so1der/ivl275_clock/ivl275_schematic/ivl275_clock.kicad_sch

## KiCad design ivl275_schematic/ivl275_clock.kicad_sch (2024-07-03)

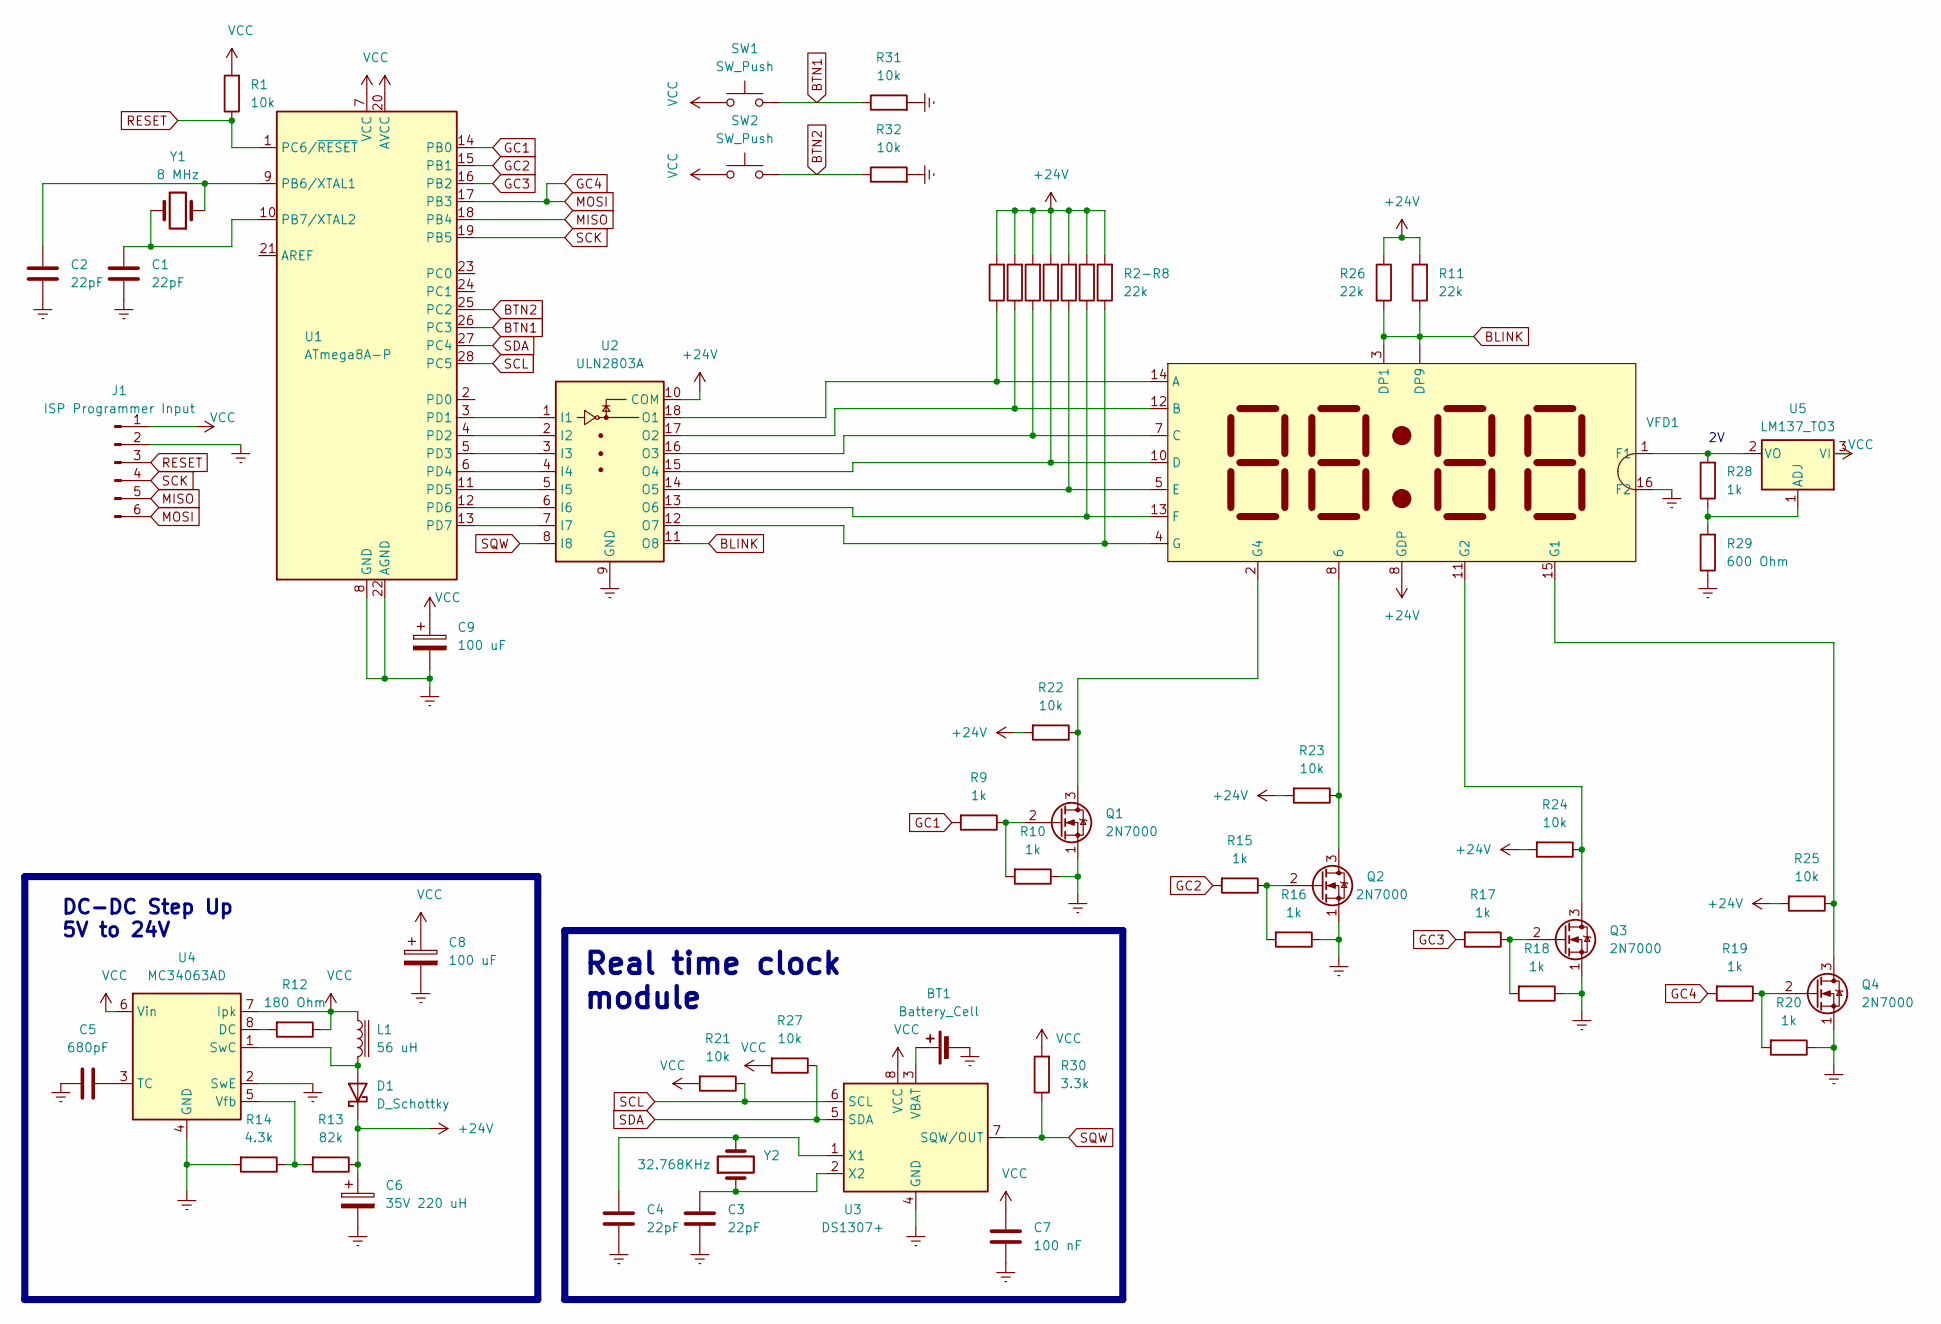
[picture p6: schematic ivl275_clock.kicad_sch]

Parts:
BT1: Battery_Cell
C1, C2, C3, C4: 22pF; C_Disc_D4.7mm_W2.5mm_P5.00mm
C5: 680pF
C6: 35V 220 uH; CP_Axial_L11.0mm_D8.0mm_P15.00mm_Horizontal
C7: 100 nF
C8, C9: 100 uF
D1: D_Schottky
J1: ISP Programmer Input
L1: 56 uH
Q1, Q2, Q3, Q4: 2N7000; TO-92_Inline
R1, R21, R22, R23, R24, R25, R27: 10k
R2, R2-R8, R3, R4, R5, R6, R7, R11, R26: 22k
R9, R10, R15, R16, R17, R18, R19, R20, R28: 1k
R12: 180 Ohm
R13: 82k
R14: 4.3k
R29: 600 Ohm
R30: 3.3k
R31, R32: 10k; R_0805_2012Metric_Pad1.20x1.40mm_HandSolder
SW1, SW2: SW_Push; SW_PUSH_6mm_H5mm
U1: ATmega8A-P; DIP-28_W7.62mm
U2: ULN2803A
U3: DS1307+; DIP-8_W7.62mm
U4: MC34063AD; SOIC-8_3.9x4.9mm_P1.27mm
U5: LM137_TO3; TO-3
VFD1: (no value)
Y1: 8 MHz
Y2: 32.768KHz

Connections:
+24V: C6.1, D1.1 (K), R2.2, R2-R8.2, R3.2, R4.2, R5.2, R6.2, R7.2, R11.2, R13.1, R22.2, R23.2, R24.2, R25.2, R26.1, U2.10 (COM), VFD1.8 (6)
BLINK: R11.1, R26.2, U2.11 (O8), VFD1. (DP9), VFD1.3 (DP1)
BTN1: R31.1, SW1.2, U1.26 (PC3)
BTN2: R32.1, SW2.2, U1.25 (PC2)
Earth: BT1.2 (-), C1.2, C2.2, C3.2, C4.2, C5.1, C6.2, C7.2, C8.2, C9.2, J1.2, Q1.1 (S), Q2.1 (S), Q3.1 (S), Q4.1 (S), R10.1, R14.2, R16.1, R18.1, R20.1, R29.1, R31.2, R32.2, U1.8 (GND), U1.22 (AGND), U2.9 (GND), U3.4 (GND), U4.2 (SwE), U4.4 (GND), VFD1.16 (F2)
GC1: R9.2, U1.14 (PB0)
GC2: R15.2, U1.15 (PB1)
GC3: R17.2, U1.16 (PB2)
GC4: J1.6, R19.2, U1.17 (PB3)
MISO: J1.5, U1.18 (PB4)
unnamed: BT1.1 (+), U3.3 (VBAT)
unnamed: C1.1, U1.10 (PB7/XTAL2), Y1.2
unnamed: C2.1, U1.9 (PB6/XTAL1), Y1.1
unnamed: C3.1, U3.2 (X2), Y2.1
unnamed: C4.1, U3.1 (X1), Y2.2
unnamed: C5.2, U4.3 (TC)
unnamed: D1.2 (A), L1.2, U4.1 (SwC)
unnamed: Q1.2 (G), R9.1, R10.2
unnamed: Q1.3 (D), R22.1, VFD1.2 (G4)
unnamed: Q2.2 (G), R15.1, R16.2
unnamed: Q2.3 (D), R23.1, VFD1.8 (6)
unnamed: Q3.2 (G), R17.1, R18.2
unnamed: Q3.3 (D), R24.1, VFD1.11 (G2)
unnamed: Q4.2 (G), R19.1, R20.2
unnamed: Q4.3 (D), R25.1, VFD1.15 (G1)
unnamed: R2.1, U2.18 (O1), VFD1.14 (A)
unnamed: R2-R8.1, U2.12 (O7), VFD1.4 (G)
unnamed: R3.1, U2.17 (O2), VFD1.12 (B)
unnamed: R4.1, U2.16 (O3), VFD1.7 (C)
unnamed: R5.1, U2.15 (O4), VFD1.10 (D)
unnamed: R6.1, U2.14 (O5), VFD1.5 (E)
unnamed: R7.1, U2.13 (O6), VFD1.13 (F)
unnamed: R12.2, U4.8 (DC)
unnamed: R13.2, R14.1, U4.5 (Vfb)
unnamed: R28.1, R29.2, U5.1 (ADJ)
unnamed: R28.2, U5.2 (VO), VFD1.1 (F1)
unnamed: U1.3 (PD1), U2.1 (I1)
unnamed: U1.4 (PD2), U2.2 (I2)
unnamed: U1.5 (PD3), U2.3 (I3)
unnamed: U1.6 (PD4), U2.4 (I4)
unnamed: U1.11 (PD5), U2.5 (I5)
unnamed: U1.12 (PD6), U2.6 (I6)
unnamed: U1.13 (PD7), U2.7 (I7)
RESET: J1.3, R1.1, U1.1 (PC6/~RESET)
SCK: J1.4, U1.19 (PB5)
SCL: R21.1, U1.28 (PC5), U3.6 (SCL)
SDA: R27.1, U1.27 (PC4), U3.5 (SDA)
SQW: R30.1, U2.8 (I8), U3.7 (SQW/OUT)
VCC: C7.1, C8.1, C9.1, J1.1, L1.1, R1.2, R12.1, R21.2, R27.2, R30.2, SW1.1, SW2.1, U1.7 (VCC), U1.20 (AVCC), U3.8 (VCC), U4.6 (Vin), U4.7 (Ipk), U5.3 (VI)

Notes on the sheet:
DC-DC Step Up 5V to 24V
Real time clock module
